Fri3dCamp/badge/datasheets/tactile-switch.jpg

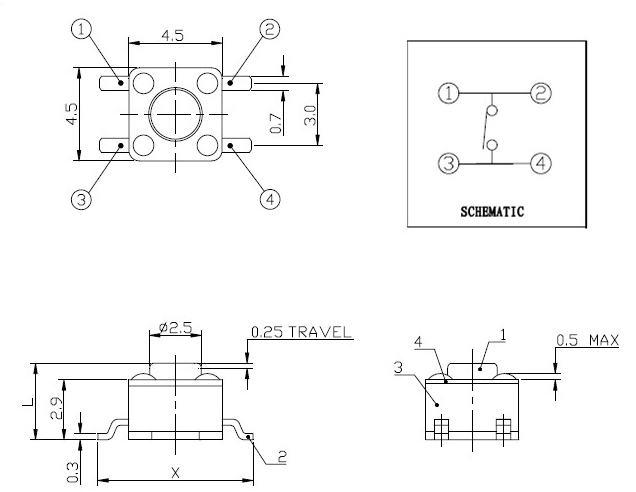
datasheets/tactile-switch.jpg
